renata7zemanova/Logic/text/text/literatura.tex

% Pro sazbu seznamu literatury použijte jednu z následujících možností

%%%%%%%%%%%%%%%%%%%%%%%%%%%%%%%%%%%%%%%%%%%%%%%%%%%%%%%%%%%%%%%%%%%%%%%%%
%1) Seznam citací definovaný přímo pomocí prostředí literatura / thebibliography

\begin{thebibliography}{99}
\bibitem{Kalkulacka_drahy_DPS}
    ADVANCED CIRCUITS:
    \emph{PCB Trace Width Calculator}
    Denver, Colorado: [cit.\,09.\,12.\,2020].
    Dostupné z~URL:\\
    <\url{https://www.4pcb.com/trace-width-calculator.html}>.

\bibitem{Logic_deskovka}
    Agátin svět:
    \emph{Dřevěná hra Logik}
    Praha: [cit.\,08.\,12.\,2020].
    Dostupné z~URL:\\
    <\url{https://www.agatinsvet.cz/drevena-hra-logik/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}>.

\bibitem{Nedostatek_soucastek}
    Chiptron, Petrus:
    \emph{Součástky nejsou. Rok 2021 nevypadá pro bastlíře vůbec dobře.}
    Poslední aktualizace 16.\,04.\,2021 [cit.\,07.\,05.\,2021].
    Dostupné z~URL:\\
    <\url{https://chiptron.cz/news.php?readmore=1186}>.

\bibitem{Devkit_schema}
    Espressif:
    \emph{ESP32\_DevKic\_v4}
    Poslední aktualizace 06.\,12.\,2017 [cit.\,24.\,11.\,2020].
    Dostupné z~URL:\\
    <\url{https://dl.espressif.com/dl/schematics/esp32_devkitc_v4-sch.pdf}>.

\bibitem{PICO_datasheet}
    Espressif Systems:
    \emph{ESP32-PICO-D4}
    Poslední aktualizace 2019 [cit.\,24.\,11.\,2020].
    Dostupné z~URL:\\
    <\url{https://www.espressif.com/sites/default/files/documentation/esp32-pico-d4_datasheet_en.pdf}>.

\bibitem{KiCad}
    Jean-Pierre Charras, Dick Hollenbeck, Wayne Stambaugh:
    \emph{KiCad EDA}
    [cit.\,07.\,12.\,2020].
    Dostupné z~URL:\\
    <\url{https://kicad.org/}>.

\bibitem{JLCPCB}
    JLCPCB:
    \emph{JLCPCB}
    [cit.\,23.\,11.\,2020].
    Dostupné z~URL:\\
    <\url{https://jlcpcb.com/}>.

\bibitem{JLCPCB_Capabilities}
    JLCPCB:
    \emph{PCB Capabilities}
    [cit.\,23.\,11.\,2020].
    Dostupné z~URL:\\
    <\url{https://jlcpcb.com/capabilities/Capabilities}>.

\bibitem{Logic_pravidla}
    Klub deskových her Paluba:
    \emph{Logik pravidla}
    [cit.\,30.\,11.\,2020].
    Dostupné z~URL:\\
    <\url{http://testapp.hrejsi.cz/logik/pravidla.htm}>.

\bibitem{Nabijeci_modul}
    Laskarduino:
    \emph{Nabíječka Li-ion článku TP4056 microUSB}
    [cit.\,04.\,12.\,2020].
    Dostupné z~URL:\\
    <\url{https://www.laskarduino.cz/nabijecka-li-ion-clanku-tp4056-microusb/}>.

\bibitem{USB-C}
    Microchip Technology Inc.:
    \emph{AN1953, Introduction to USB Type-C}
    Poslední aktualizace 2015 [cit.\,28.\,04.\,2021].
    Dostupné z~URL:\\
    <\url{https://cdn.sparkfun.com/assets/e/b/4/f/7/USB-C_Datasheet.pdf}>.

\bibitem{18650}
    NKON:
    \emph{INR18650-29E}
    [cit.\,01.\,12.\,2020].
    Dostupné z~URL:\\
    <\url{https://eu.nkon.nl/samsung-inr18650-29e.html}>.

\bibitem{18650_pouzdro}
    POSTAV ROBOTA:
    \emph{Držák na baterie, 2~akumulátorové články 18650 do DPS}
    [cit.\,01.\,12.\,2020].
    Dostupné z~URL:\\
    <\url{https://www.postavrobota.cz/Drzak-na-baterie-2-akumulatorove-clanky-18650-do-DPS-d644.htm}>.

\bibitem{Rezistorova_rada}
    Radioklub OK1KVK:
    \emph{Elektrotechnické řady hodnot E3, E6, E12, E24}
    Karlovy Vary [cit.\,28.\,04.\,2021].
    Dostupné z~URL:\\
    <\url{https://ok1kvk.cz/clanek/2011/elektrotechnicke-rady-hodnot-e3-e6-e12-e24/}>.

\bibitem{SmartLeds}
    RoboticsBrno, Jan Mrázek:
    \emph{SmartLeds}
    Brno: Poslední aktualizace 27.\,04.\,2021 [cit.\,08.\,05.\,2021].
    Dostupné z~URL:\\
    <\url{https://github.com/RoboticsBrno/SmartLeds}>.

\bibitem{UniversalStepDown}
    RoboticsBrno, Jan Mrázek:
    \emph{RB0005-UniversalStepDown}
    Brno: Poslední aktualizace 30.\,11.\,2020 [cit.\,04.\,12.\,2020].
    Dostupné z~URL:\\
    <\url{https://github.com/RoboticsBrno/RB0005-UniversalStepDown}>.

\bibitem{TP4056_datasheet}
    Satic Chipid:
    \emph{TP4056 A~Standalone Linear Li-lon Battery Charger with Thermal Regulation in SOP-8 }
    [cit.\,03.\,12.\,2020].
    Dostupné z~URL:\\
    <\url{https://static.chipdip.ru/lib/977/DOC002977110.pdf}>.

\bibitem{SY8105_datasheet}
    SILERGY:
    \emph{Applocation Note:AN\_SY8105}
    [cit.\,24.\,11.\,2020].
    Dostupné z~URL:\\
    <\url{https://datasheet.lcsc.com/szlcsc/Silergy-Corp-SY8105ADC_C178247.pdf}>.

\bibitem{CP2102_datasheet}
    Silicon Laboratories Inc.:
    \emph{CP2102N Data Sheet}
    USA: Poslední aktualizace květen 2016 [cit.\,24.\,11.\,2020].
    Dostupné z~URL:\\
    <\url{https://www.silabs.com/documents/public/data-sheets/cp2102n-datasheet.pdf}>.

\bibitem{WS2812C_datasheet}
    Worldsemi:
    \emph{WS2812C}
    Poslední aktualizace 06.\,12.\,2017 [cit.\,24.\,11.\,2020].
    Dostupné z~URL:\\
    <\url{https://datasheet.lcsc.com/szlcsc/1810231210_Worldsemi-WS2812C_C114587.pdf}>.

%%%	
\bibitem{sr02/2009}
		VUT v~Brně:
    \emph{Úprava, odevzdávání a zveřejňování vysokoškolských kva\-li\-fi\-kač\-ních prací na VUT v~Brně}\/ [online].
		Směrnice rektora č.\,2/2009.
		Brno: 2009, po\-sled\-ní aktualizace 24.\,3.\,2009 [cit.\,23.\,10.\,2015].
    Dostupné z~URL:\\
    <\url{https://www.vutbr.cz/uredni-deska/vnitrni-predpisy-a-dokumenty/smernice-rektora-f34920/}>.

\bibitem{CSN_ISO_690-2011}
    \emph{ČSN ISO 690 (01 0197) Informace a dokumentace -- Pravidla pro bibliografické odkazy a citace informačních zdrojů.}
    40 stran. Praha: Český normalizační institut, 2011.

\bibitem{CSN_ISO_7144-1997}
    \emph{ČSN ISO 7144 (010161) Dokumentace -- Formální úprava disertací a podobných dokumentů.}
    24 stran. Praha: Český normalizační institut, 1997.

\bibitem{CSN_ISO_31-11}
    \emph{ČSN ISO 31-11 Veličiny a jednotky -- část 11: Matematické znaky a značky používané ve fyzikálních vědách a v~technice.}
    Praha: Český normalizační institut, 1999.

\bibitem{BiernatovaSkupa2011:CSNISO690komentar}
    BIERNÁTOVÁ, O., SKŮPA, J.:
    \emph{Bibliografické odkazy a citace dokumentů dle ČSN ISO 690 (01 0197) platné od 1.\,dubna 2011}\/ [online].
    2011, poslední aktualizace 2.\,9.\,2011 [cit. 19.\,10.\,2011].
    Dostupné z~URL:
    \(<\)\url{http://www.citace.com/CSN-ISO-690.pdf}\(>\)
%    \(<\)\href{http://www.boldis.cz/citace/citace.html}{http://www.boldis.cz/citace/citace.html}\(>\).

\bibitem{pravidla}
    \emph{Pravidla českého pravopisu}.
    Zpracoval kolektiv autorů. 1.\ vydání.
    Olomouc: FIN PUB\-LISH\-ING, 1998. 575 s. ISBN 80-86002-40-3.

\bibitem{Walter1999}
	WALTER, G.\,G.; SHEN, X.
	\emph{Wavelets and Other Orthogonal Systems}.
	2. vyd. Boca Raton: Chapman\,\&\,Hall/CRC, 2000. 392~s. ISBN 1-58488-227-1

\bibitem{Svacina1999IEEE}
	SVAČINA, J.
	Dispersion Characteristics of Multilayered Slotlines -- a Simple Approach.
	\emph{IEEE Transactions on Microwave Theory and Techniques},
	1999, vol.\,47, no.\,9, s.\,1826--1829. ISSN 0018-9480.

\bibitem{RajmicSysel2002}
    RAJMIC, P.; SYSEL, P.
    Wavelet Spectrum Thresholding Rules.
    In \emph{Proceedings of the International Conference Research in Telecommunication Technology},
    Žilina: Žilina University, 2002. s.\,60--63. ISBN 80-7100-991-1.

\end{thebibliography}

%%%%%%%%%%%%%%%%%%%%%%%%%%%%%%%%%%%%%%%%%%%%%%%%%%%%%%%%%%%%%%%%%%%%%%%%%
%%2) Seznam citací pomocí BibTeXu
%% Při použití je nutné v TeXnicCenter ve výstupním profilu aktivovat spouštění BibTeXu po překladu.
%% Definice stylu seznamu
%\bibliographystyle{unsrturl}
%% Pro českou sazbu lze použít styl czechiso.bst ze stránek
%% http://www.fit.vutbr.cz/~martinek/latex/czechiso.tar.gz
%%\bibliographystyle{czechiso}
%% Vložení souboru se seznamem citací
%\bibliography{text/literatura}
%
%% Následující příkaz je pouze pro ukázku sazby literatury při použití BibTeXu.
%% Způsobí citaci všech zdrojů v souboru literatura.bib, i když nejsou citovány v textu.
%\nocite{*}
