renata7zemanova/Logic/HW/blokove_schema.jpg

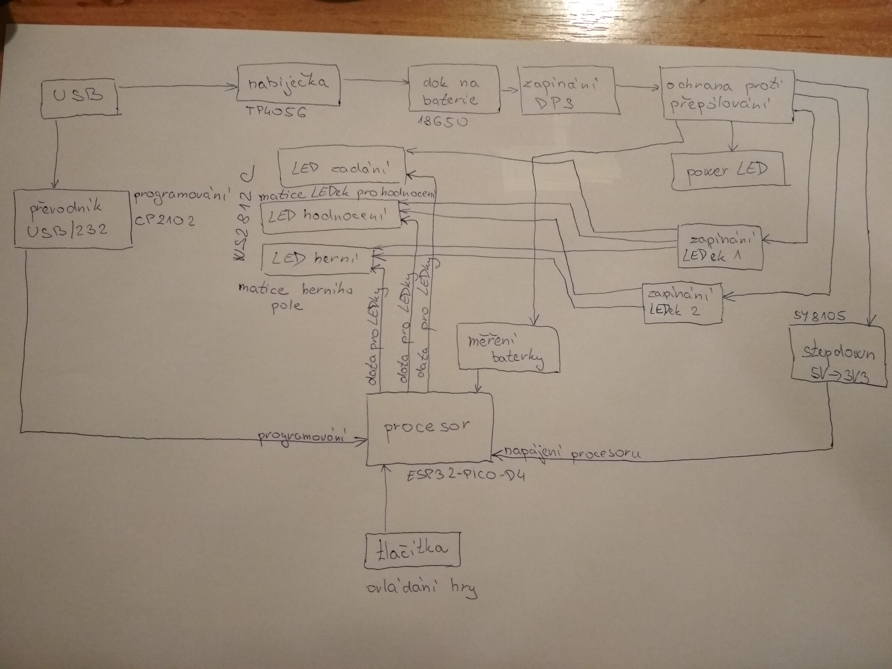
HW/blokove_schema.jpg
