renata7zemanova/Logic/text/prilohy/v1_blokove_schema.jpg

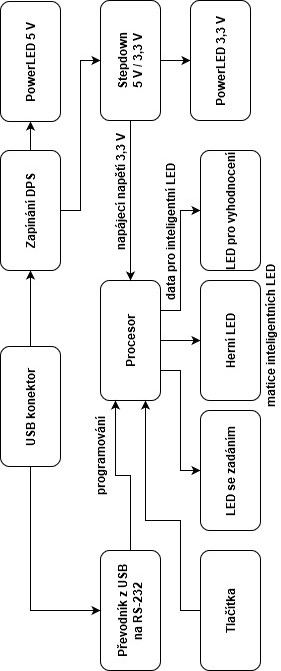
text/prilohy/v1_blokove_schema.jpg
