renata7zemanova/Logic/text/prilohy/v2_blokove_schema.jpg

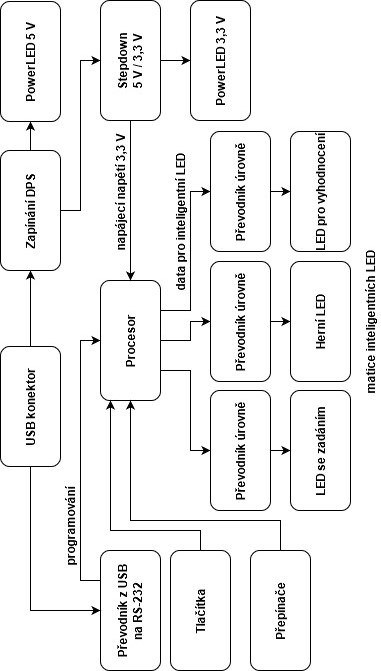
text/prilohy/v2_blokove_schema.jpg
