renata7zemanova/Logic/text/prilohy/Verze1_vrstva_Cu_BOTTOM.png

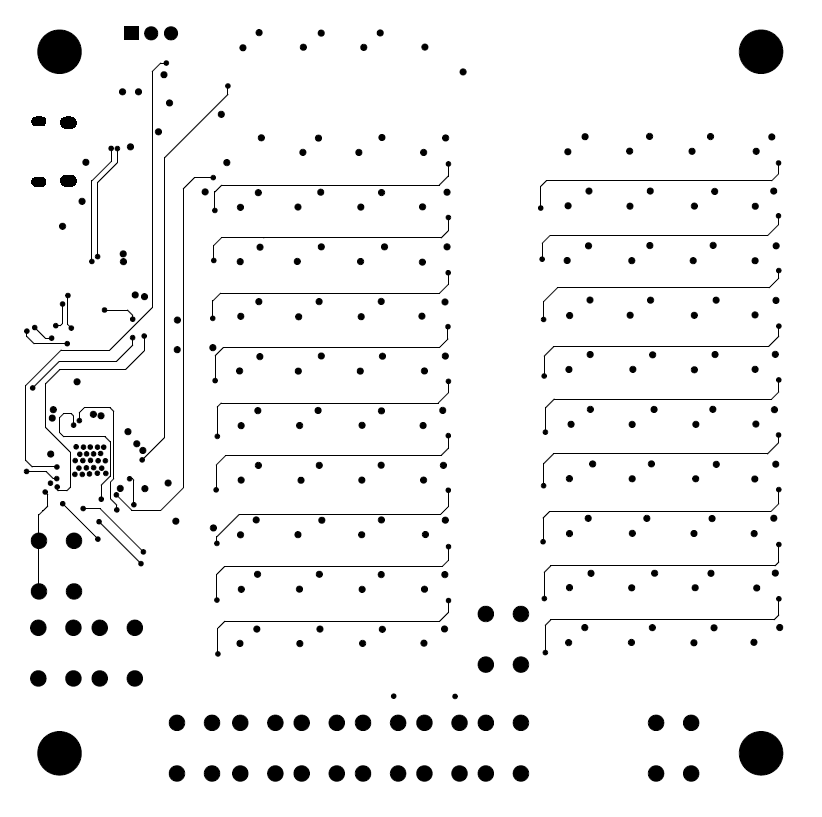
text/prilohy/Verze1_vrstva_Cu_BOTTOM.png
