renata7zemanova/Logic/text/prilohy/Verze1_vrstva_Cu_vnitrni_1.png

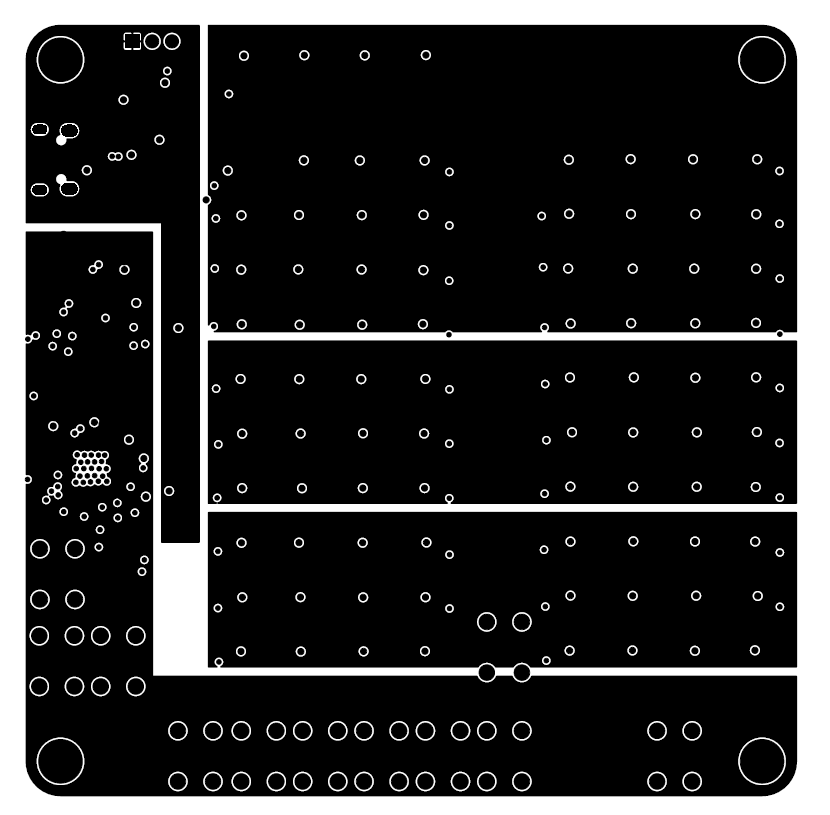
text/prilohy/Verze1_vrstva_Cu_vnitrni_1.png
