renata7zemanova/Logic/text/prilohy/Verze1_vrstva_Cu_vnitrni_GND.png

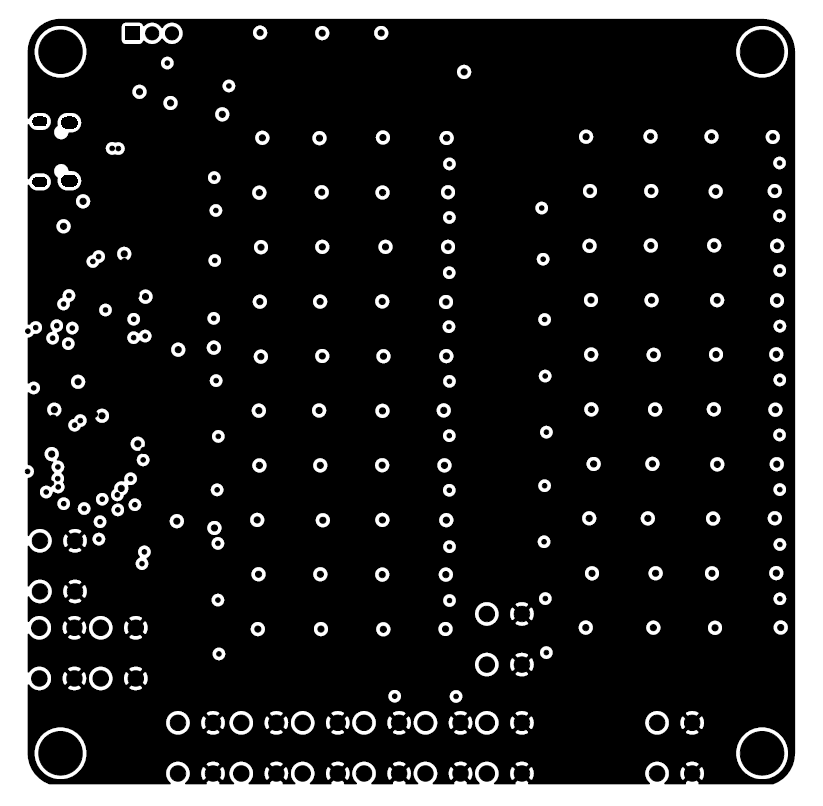
text/prilohy/Verze1_vrstva_Cu_vnitrni_GND.png
