renata7zemanova/Logic/text/prilohy/Verze1_vrstva_popisky_TOP.png

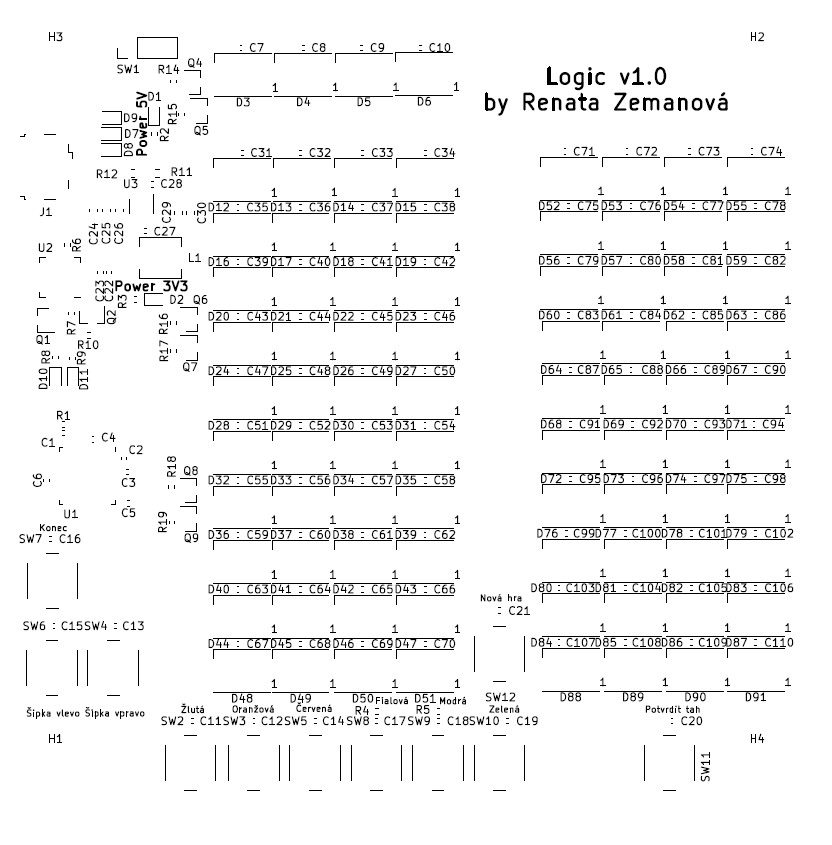
text/prilohy/Verze1_vrstva_popisky_TOP.png
