renata7zemanova/Logic/text/prilohy/tlacitka.pdf

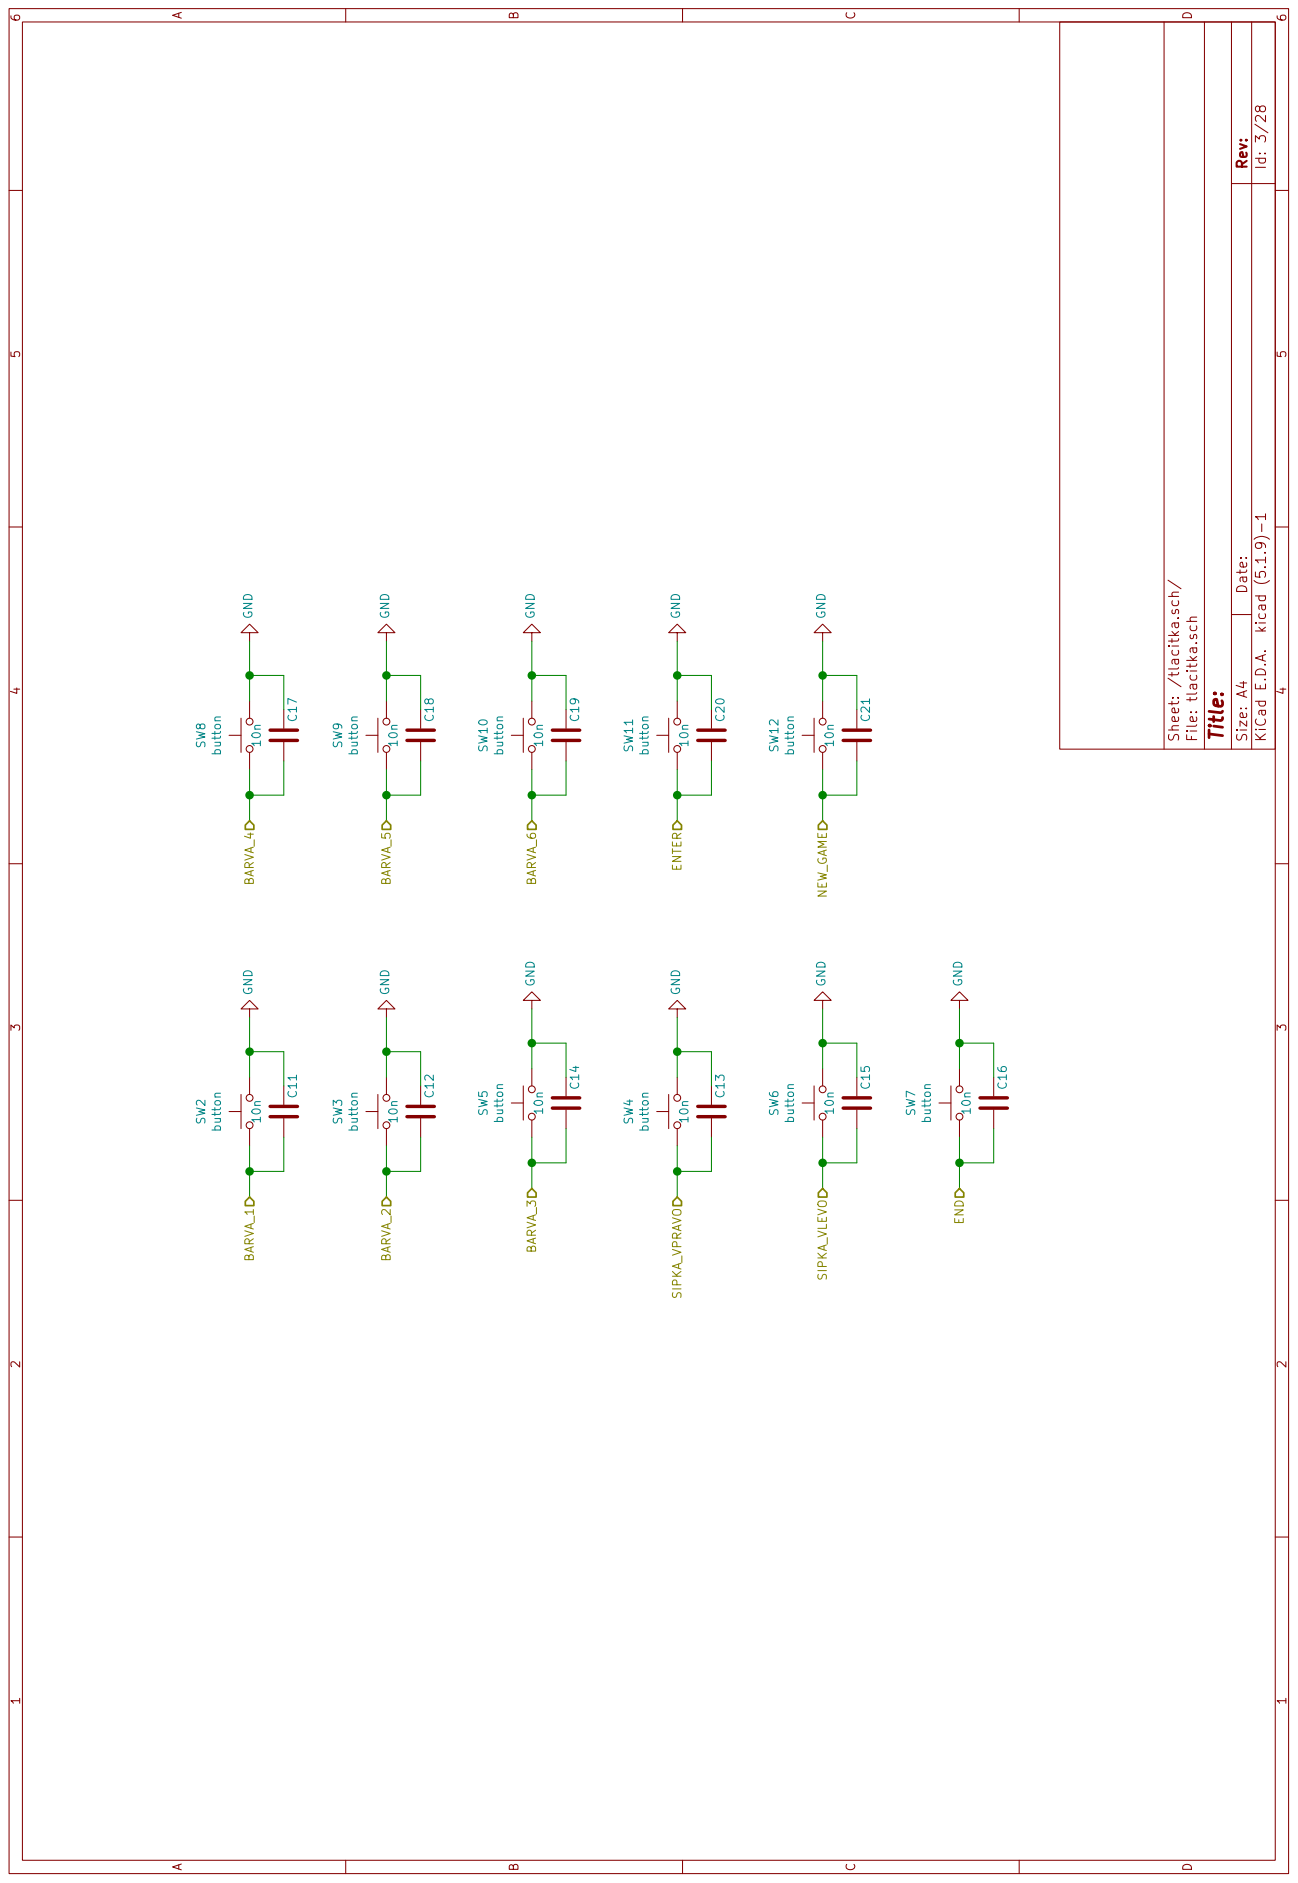
[picture p104: page 1]

D Date: KiCad E.D.A. kicad (5.1.9)-1 Rev: Size: A4

Id: 3/28 Sheet: /tlacitka.sch/ File: tlacitka.sch Title: GND GND

button GND GND GND GND GND GND GND
