renata7zemanova/Logic/text/prilohy/USBto232.pdf

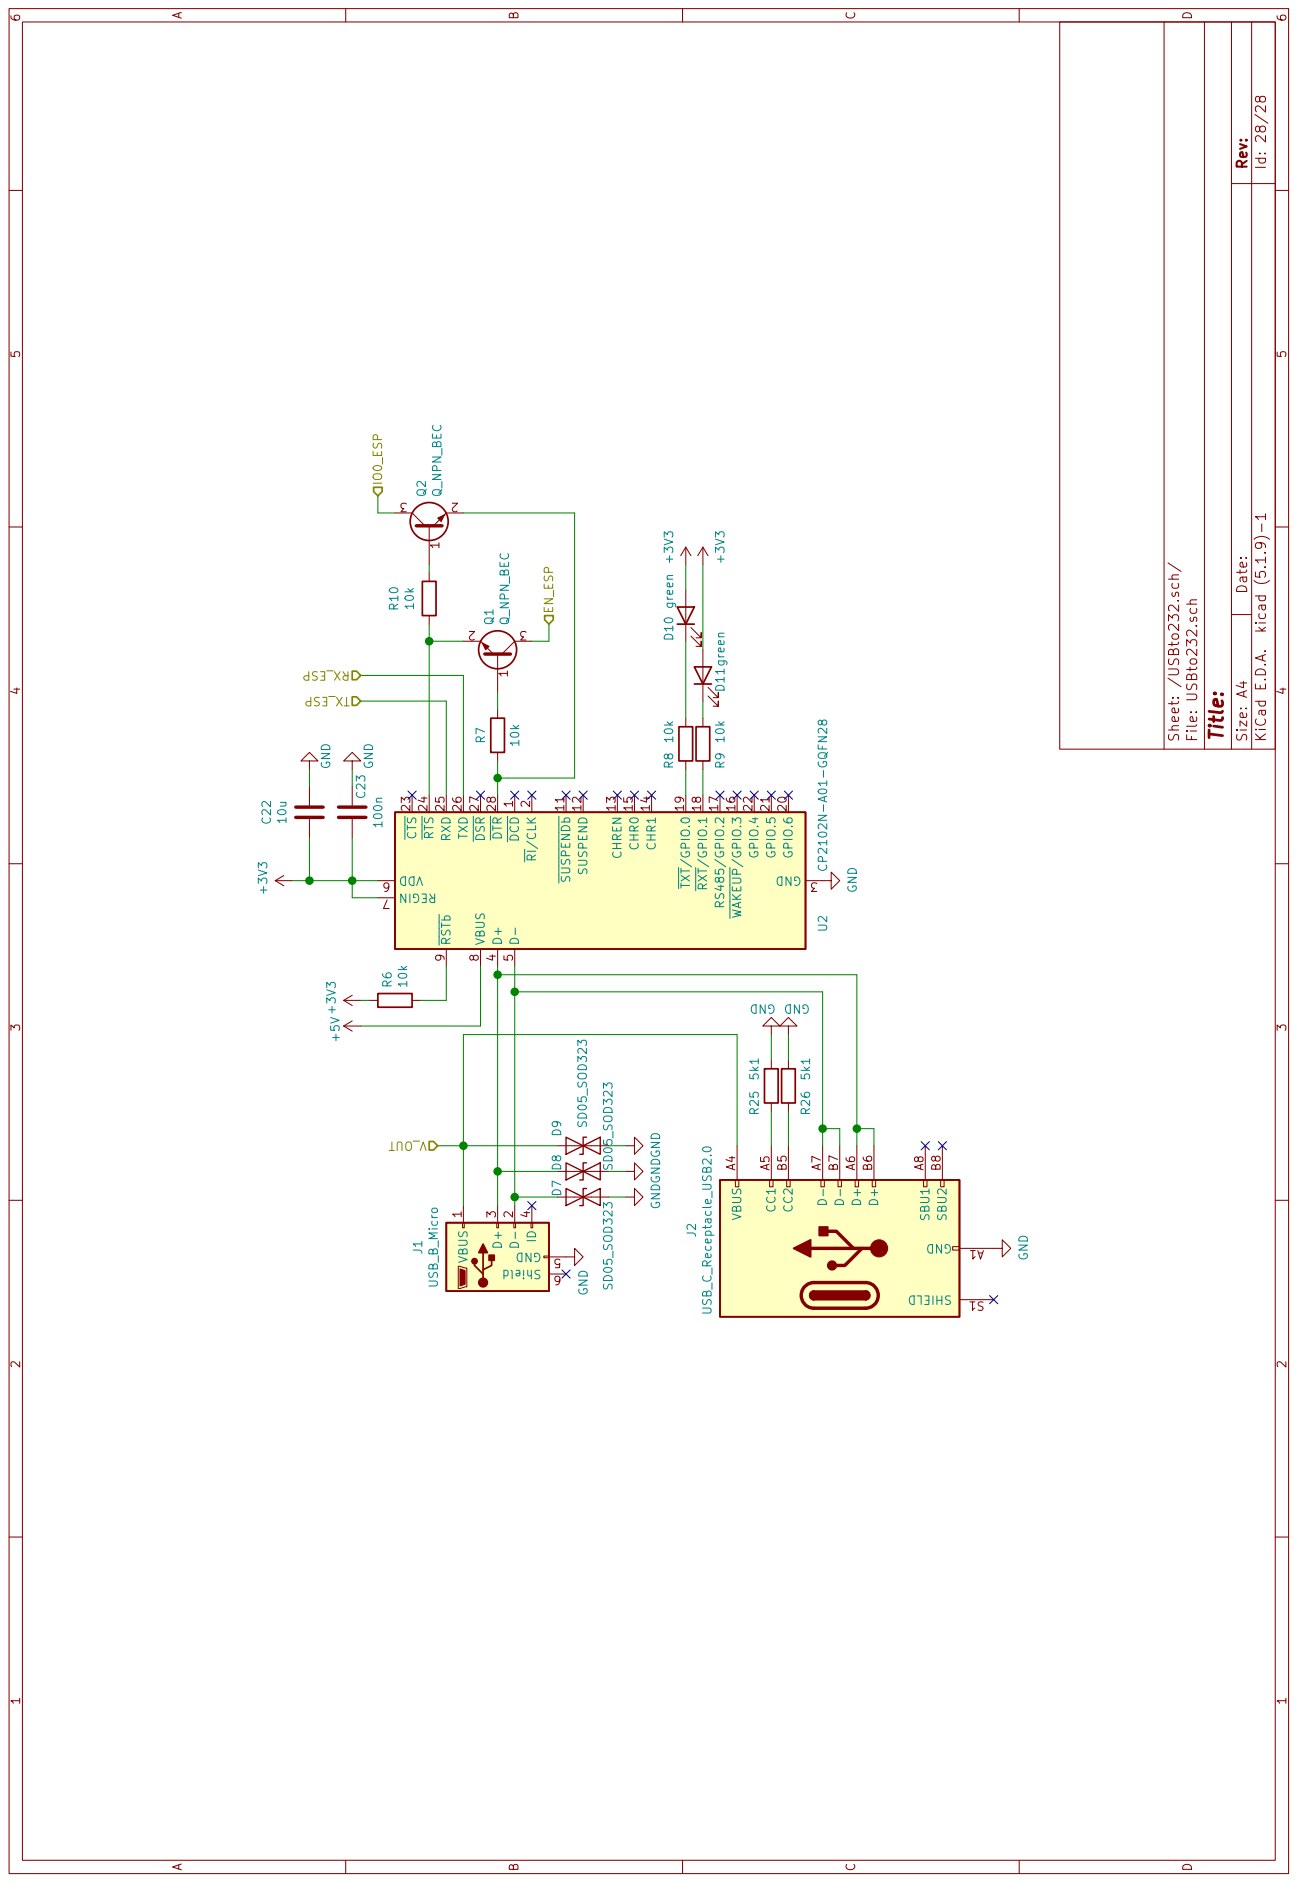
[picture p105: page 1]

D Date: KiCad E.D.A. kicad (5.1.9)-1 Rev: Size: A4

Id: 28/28 Sheet: /USBto232.sch/ File: USBto232.sch Title:

R9 10k D10 green D11 green GND A1 VBUS
