renata7zemanova/Logic/text/prilohy/zapinani_LEDek.pdf

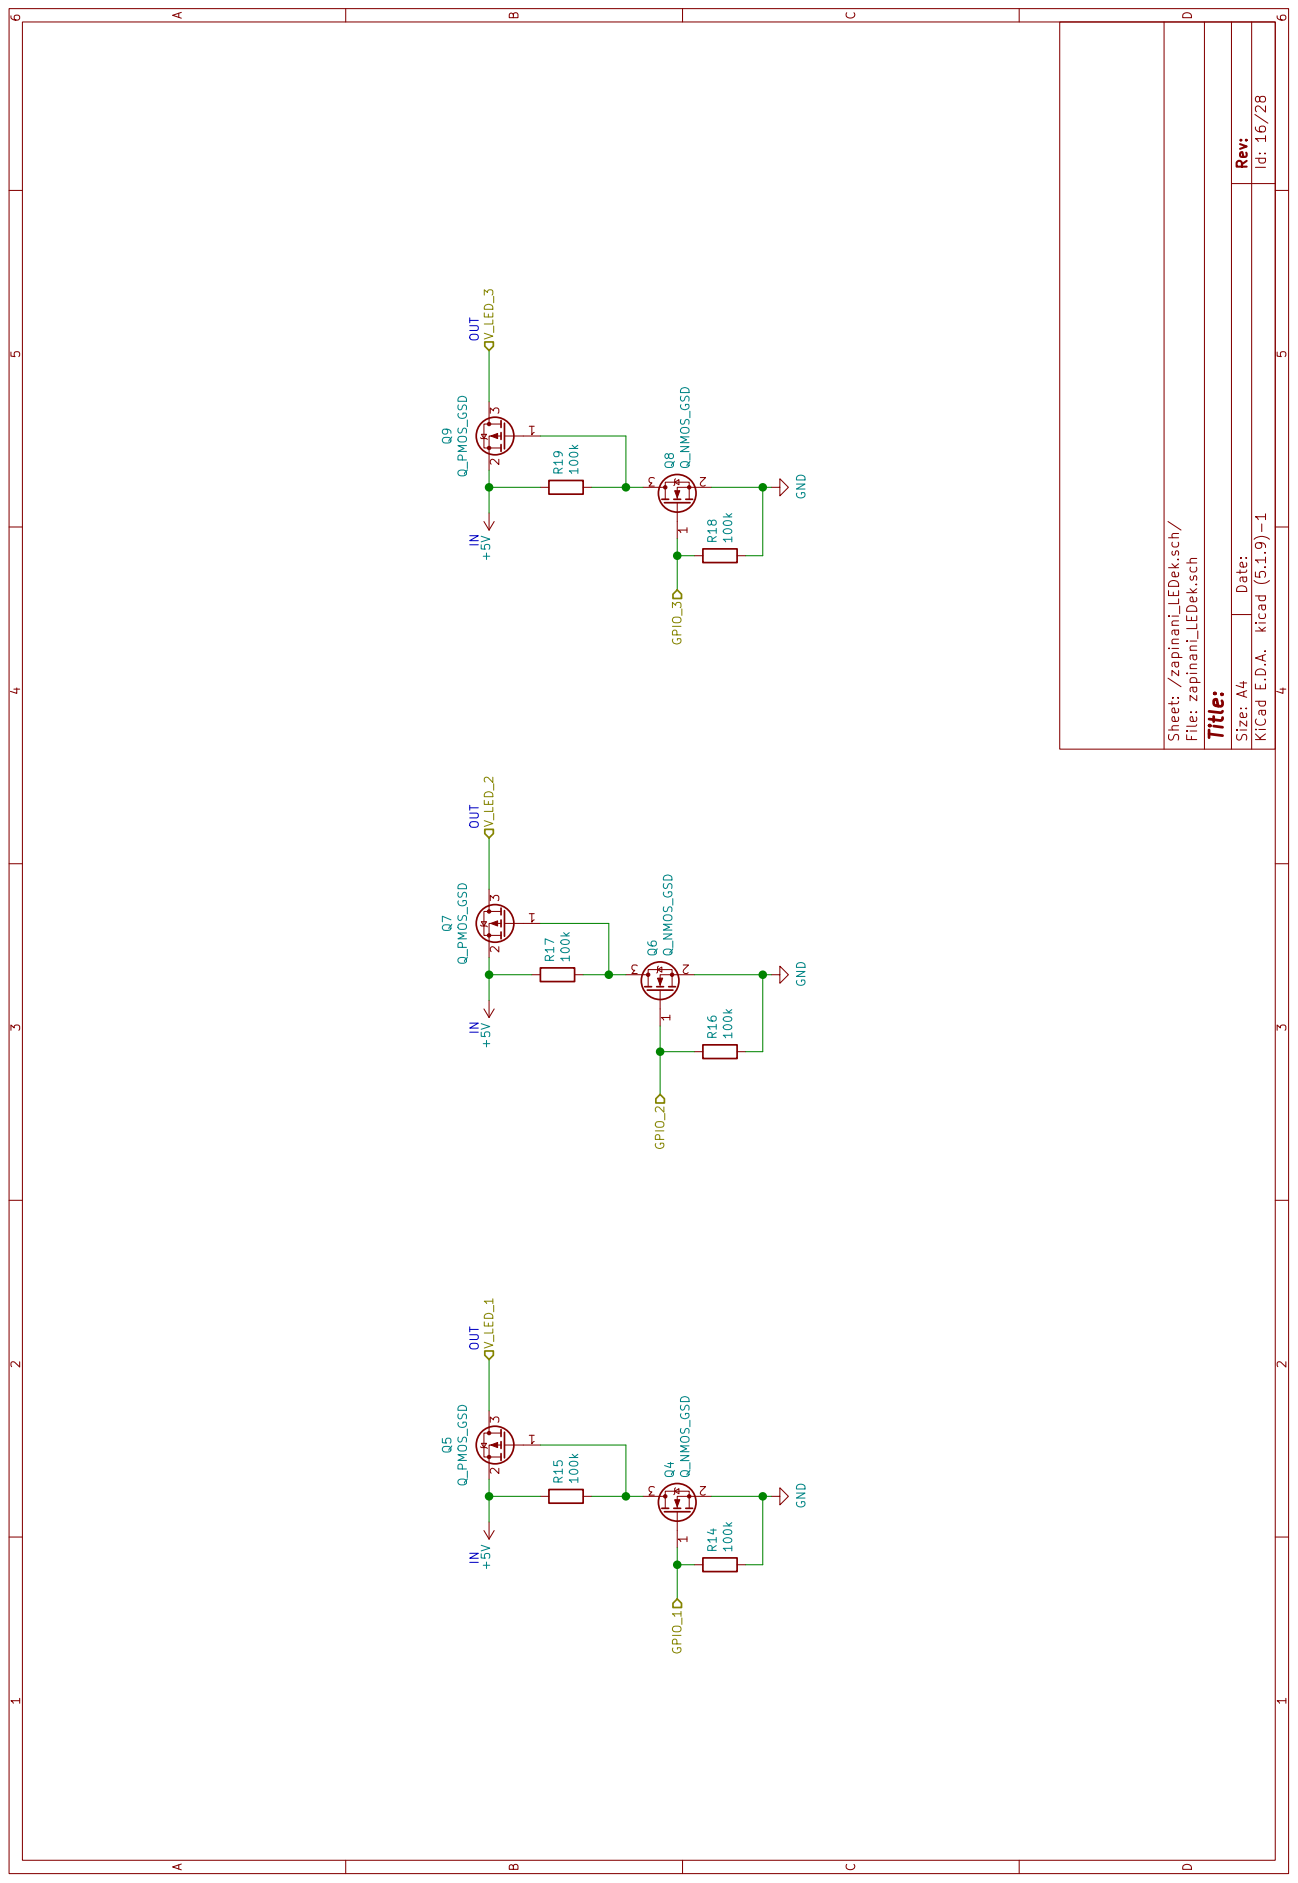
[picture p106: page 1]

D Date: KiCad E.D.A. kicad (5.1.9)-1 Rev: Size: A4

IN OUT OUT IN OUT IN
