renata7zemanova/Logic/text/logo/UMEL_color_PANTONE_CZ.pdf

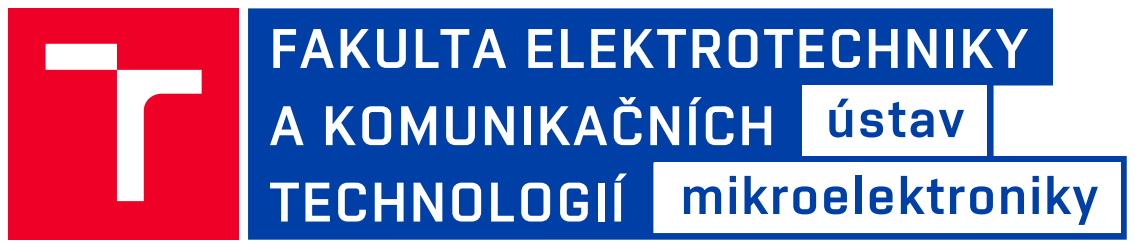
[picture p107: page 1]
